ShibamRoy9826/RoyBoard/PCB/assets/Silkscreen/levi.png

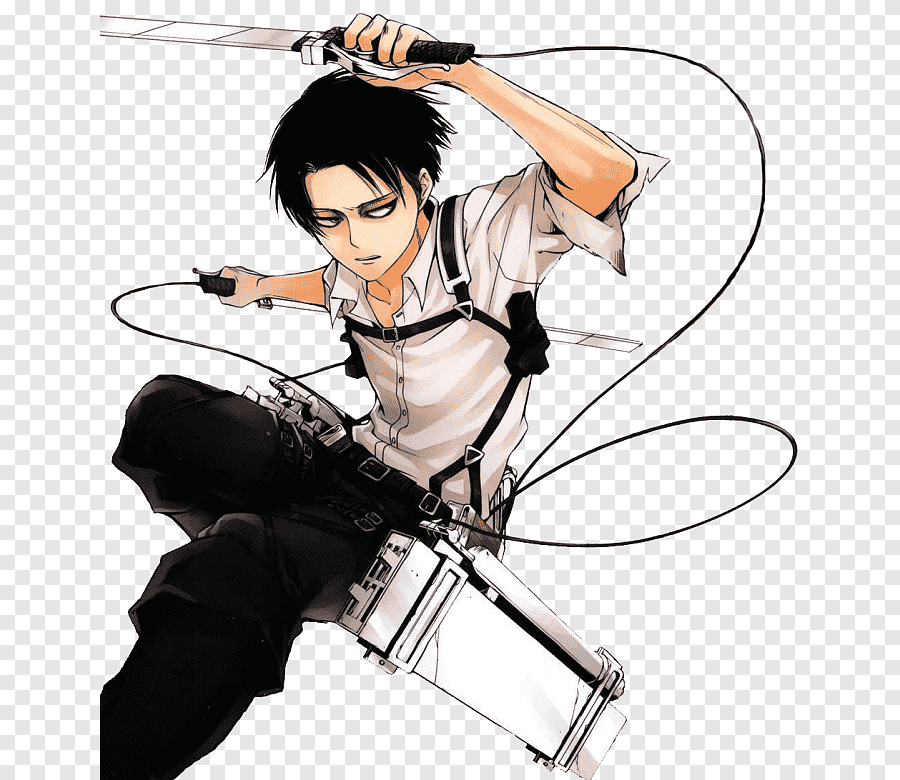
PCB/assets/Silkscreen/levi.png
