ShibamRoy9826/RoyBoard/PCB/assets/Silkscreen/neuralNetwork.jpg

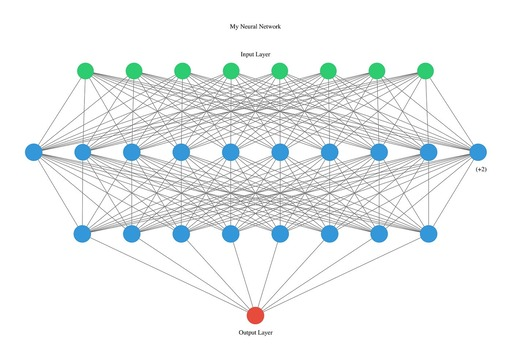
PCB/assets/Silkscreen/neuralNetwork.jpg
