ShibamRoy9826/RoyBoard/PCB/assets/Silkscreen/QR.png

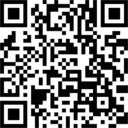
PCB/assets/Silkscreen/QR.png
