ShibamRoy9826/RoyBoard/silkscreen/creeper.png

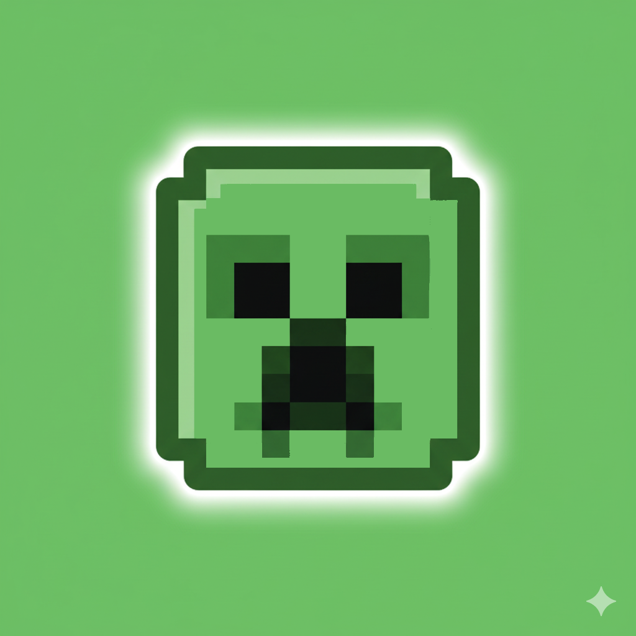
silkscreen/creeper.png
