ShibamRoy9826/RoyBoard/silkscreen/dragon.png

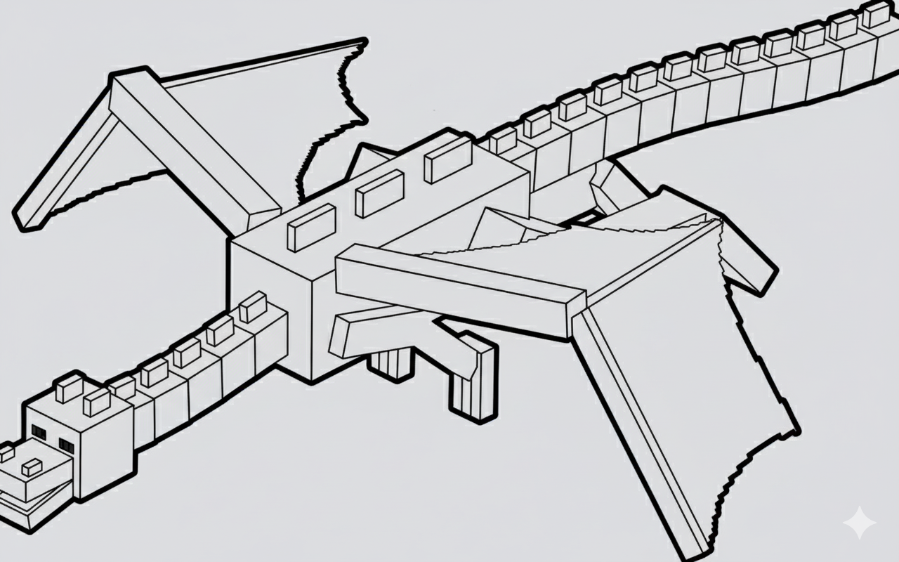
silkscreen/dragon.png
