ShibamRoy9826/RoyBoard/silkscreen/grass.jpeg

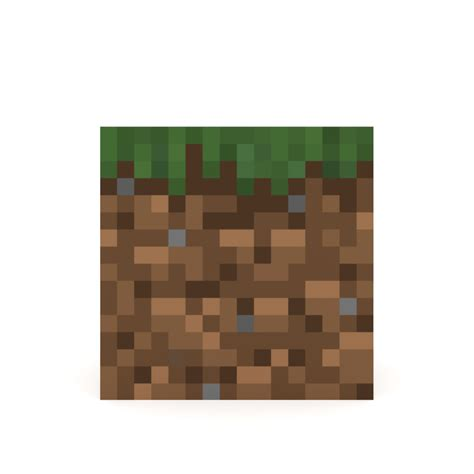
silkscreen/grass.jpeg
