ShibamRoy9826/RoyBoard/silkscreen/steve.png

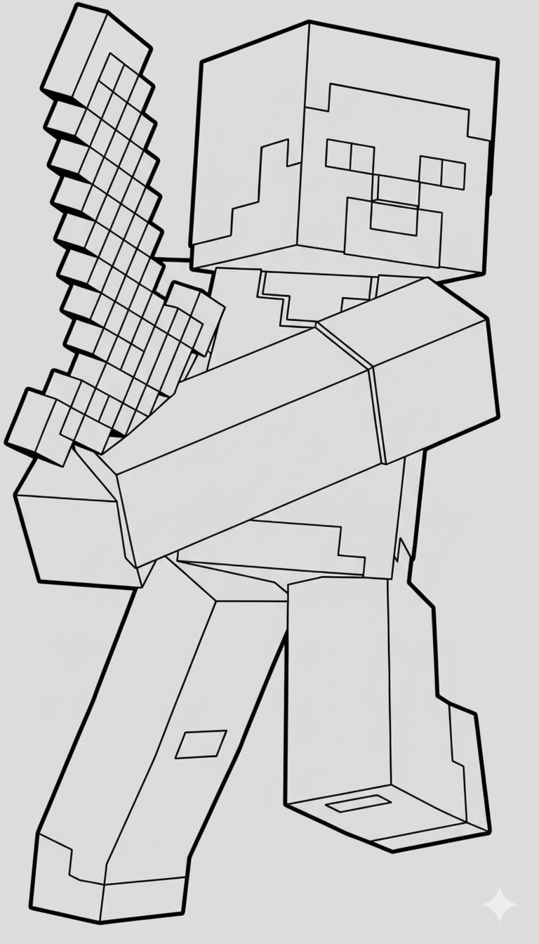
silkscreen/steve.png
