ShibamRoy9826/RoyBoard/silkscreen/sword.jpg

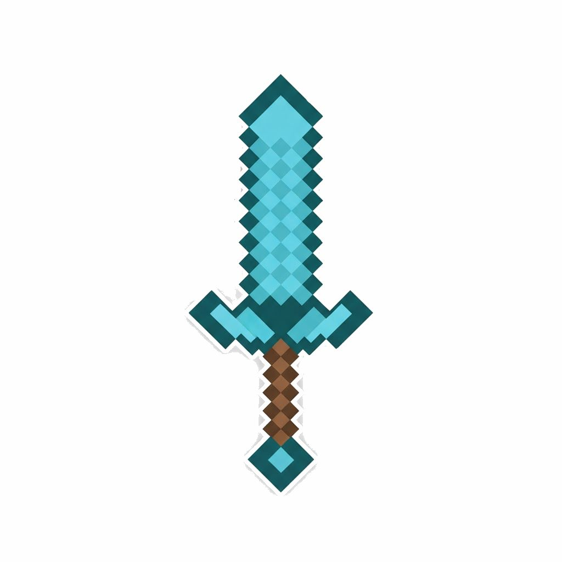
silkscreen/sword.jpg
