ShibamRoy9826/RoyBoard/PCB/assets/3d/L1, Inductor, Raspberry Pi Pico-R3.SLDPRT

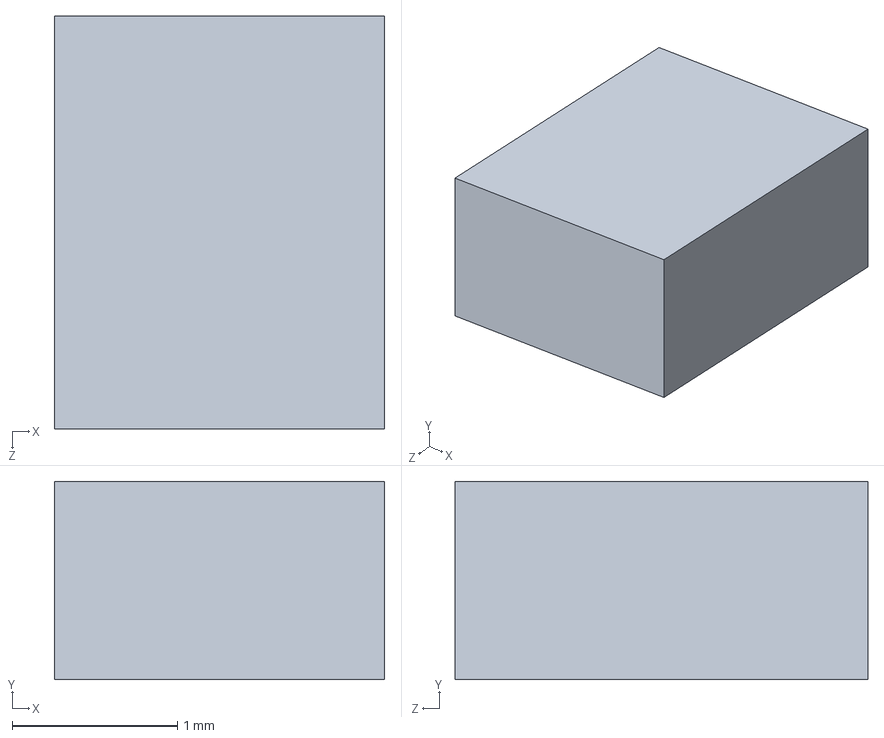
[picture p41: CAD file, 2025-03-27]
PCB/assets/3d/L1, Inductor, Raspberry Pi Pico-R3.SLDPRT
2.00 x 1.20 x 2.50 mm
