ShibamRoy9826/RoyBoard/PCB/assets/3d/SW1, Tact Switch, Raspberry Pi Pico-R3.SLDPRT

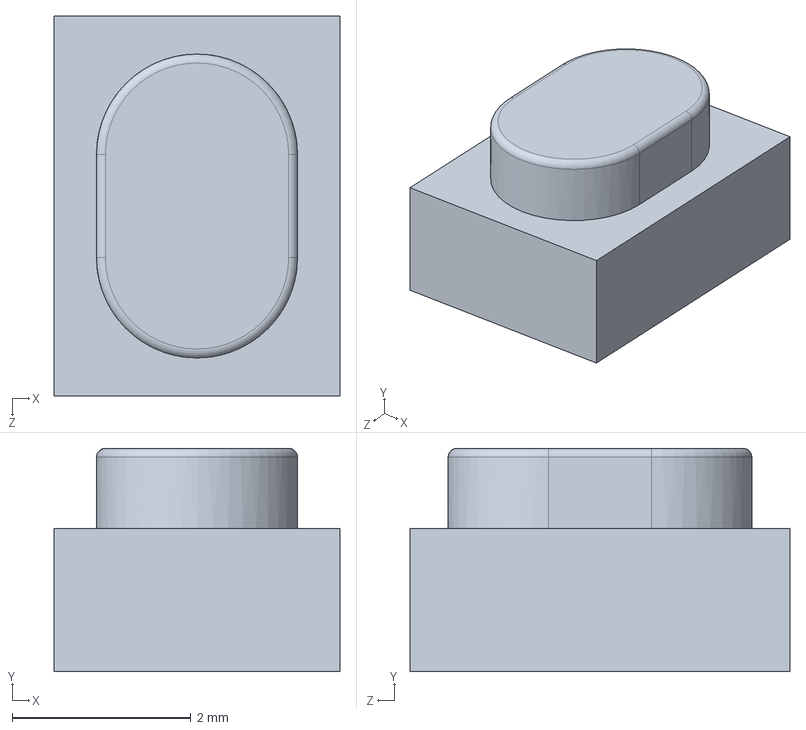
[picture p42: CAD file, 2025-03-27]
PCB/assets/3d/SW1, Tact Switch, Raspberry Pi Pico-R3.SLDPRT
3.20 x 2.50 x 4.25 mm
