ShibamRoy9826/RoyBoard/PCB/assets/3d/X1, X12M000000S096, 12 Mhz Crystal Resonator, Raspberry Pi Pico-R3.SLDPRT

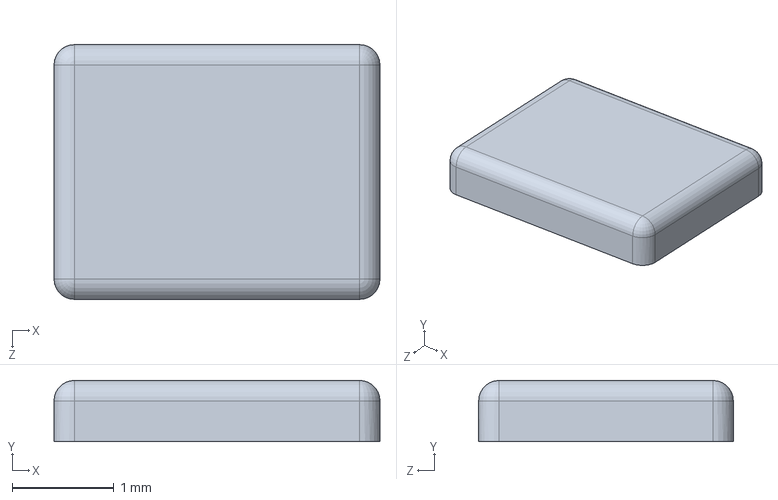
[picture p43: CAD file, 2025-03-27]
PCB/assets/3d/X1, X12M000000S096, 12 Mhz Crystal Resonator, Raspberry Pi Pico-R3.SLDPRT
3.20 x 0.6 x 2.50 mm
