ShibamRoy9826/RoyBoard/PCB/assets/3d/Q1, MOSFET, DMG1012T, Raspberry Pi Pico-R3.SLDPRT

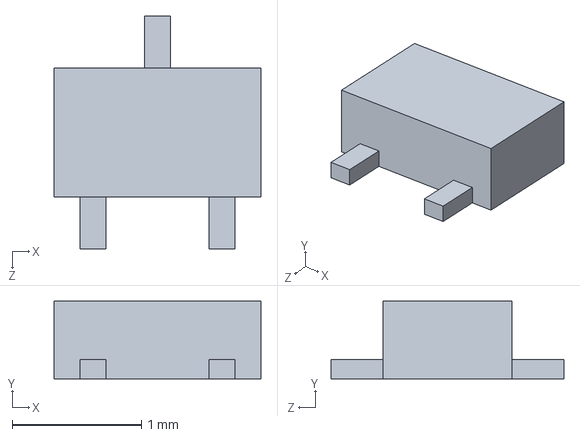
[picture p44: CAD file, 2025-03-27]
PCB/assets/3d/Q1, MOSFET, DMG1012T, Raspberry Pi Pico-R3.SLDPRT
1.60 x 0.6 x 1.80 mm
